ClimateChangeXplorers/xplorer-manual/build/stl/atmos/rs_screen_ring.stl

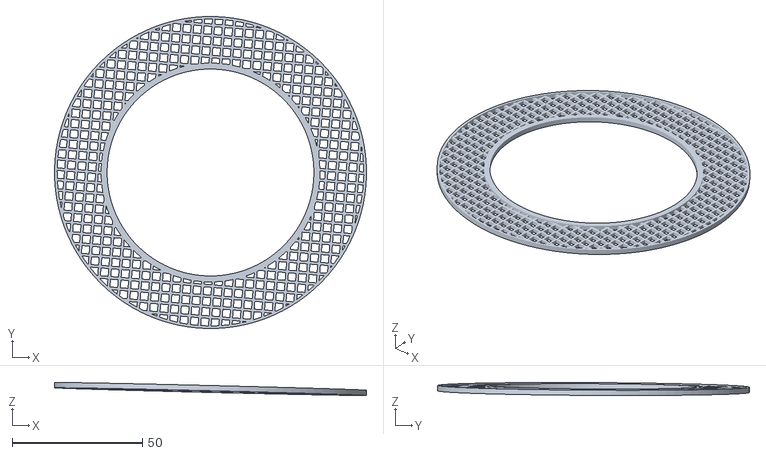
[picture p15: CAD file, 2020-08-12]
build/stl/atmos/rs_screen_ring.stl
120.0 x 120.0 x 5.02
