ClimateChangeXplorers/xplorer-manual/build/stl/hydro/hyd_rain_guage.stl

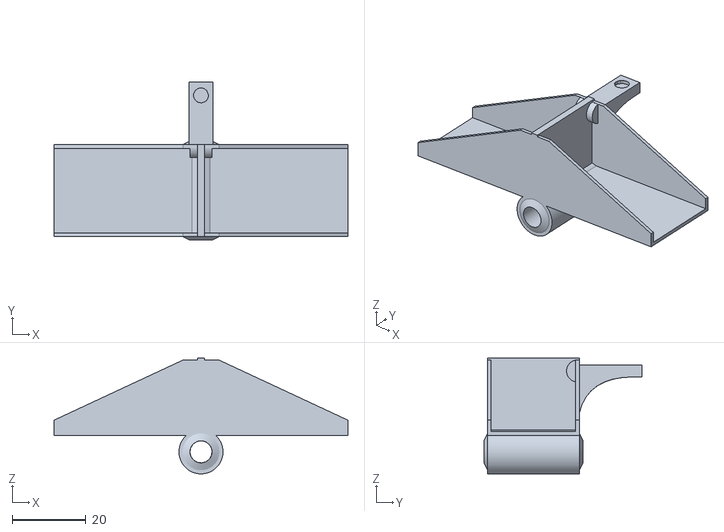
[picture p16: CAD file, 2020-07-23]
build/stl/hydro/hyd_rain_guage.stl
80.0 x 43.1 x 31.5
