ClimateChangeXplorers/xplorer-manual/build/stl/pvc/pvc_tripod_base_3.stl

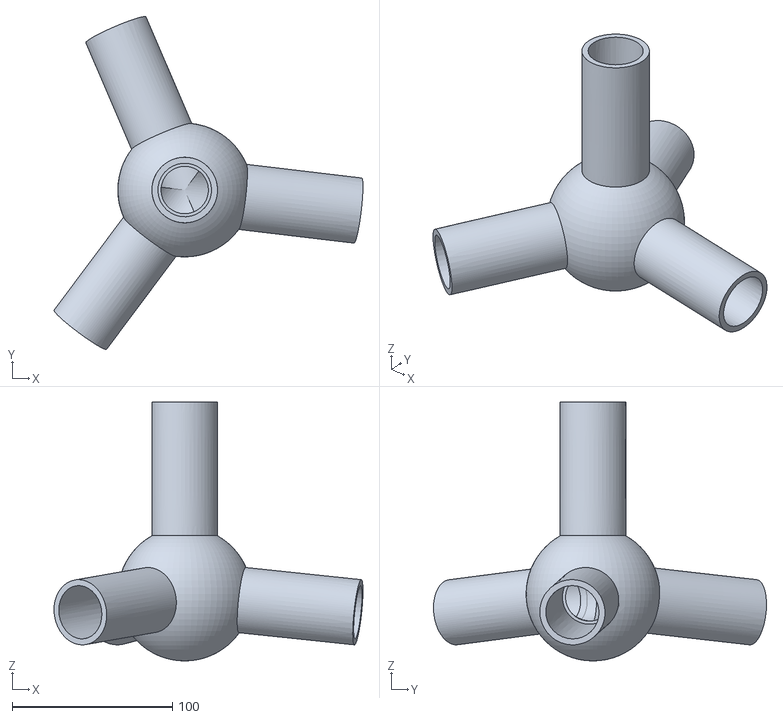
[picture p17: CAD file, 2021-01-25]
build/stl/pvc/pvc_tripod_base_3.stl
193.1 x 208.1 x 161.8
