ClimateChangeXplorers/xplorer-manual/build/stl/atmos/rs_base_plate.stl

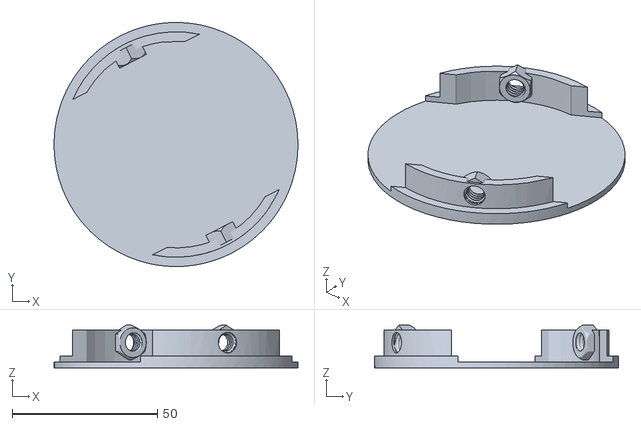
[picture p18: CAD file, 2020-08-12]
build/stl/atmos/rs_base_plate.stl
83.9 x 83.9 x 14.6
