ClimateChangeXplorers/xplorer-manual/build/stl/atmos/rs_top_leaf.stl

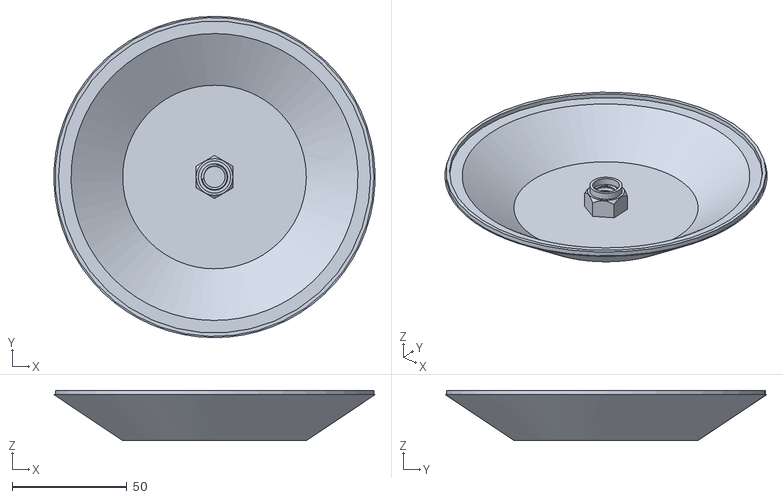
[picture p20: CAD file, 2020-07-23]
build/stl/atmos/rs_top_leaf.stl
139.8 x 139.9 x 21.9
