ClimateChangeXplorers/xplorer-manual/build/stl/pvc/pvc_stake.stl

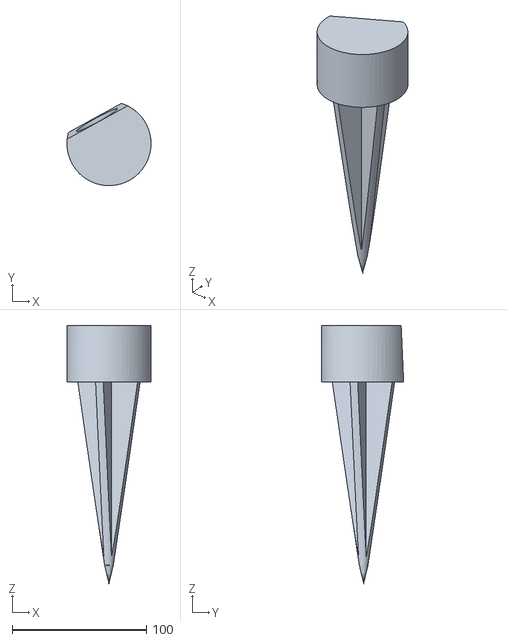
[picture p21: CAD file, 2020-11-06]
build/stl/pvc/pvc_stake.stl
62.7 x 61.4 x 192.5
