ClimateChangeXplorers/xplorer-manual/build/stl/atmos/rs_center_screen.stl

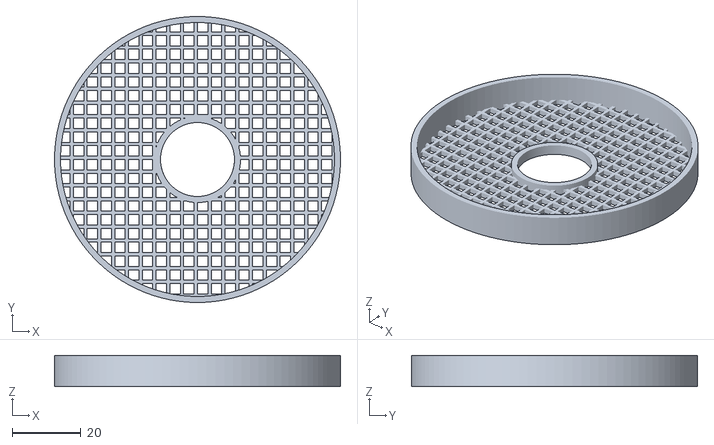
[picture p22: CAD file, 2020-07-23]
build/stl/atmos/rs_center_screen.stl
83.0 x 83.0 x 9.00
