ClimateChangeXplorers/xplorer-manual/build/stl/atmos/rs_single_leaf.stl

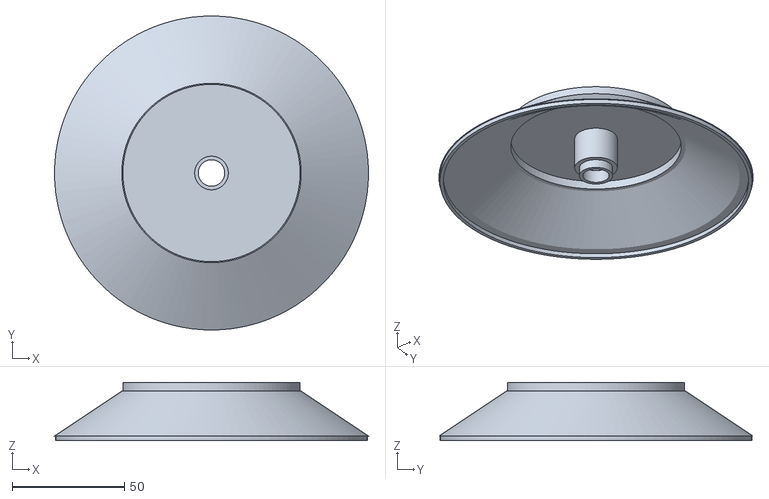
[picture p24: CAD file, 2020-07-23]
build/stl/atmos/rs_single_leaf.stl
140.0 x 140.0 x 25.9
