ClimateChangeXplorers/xplorer-manual/build/stl/pvc/pvc_en_tube.stl

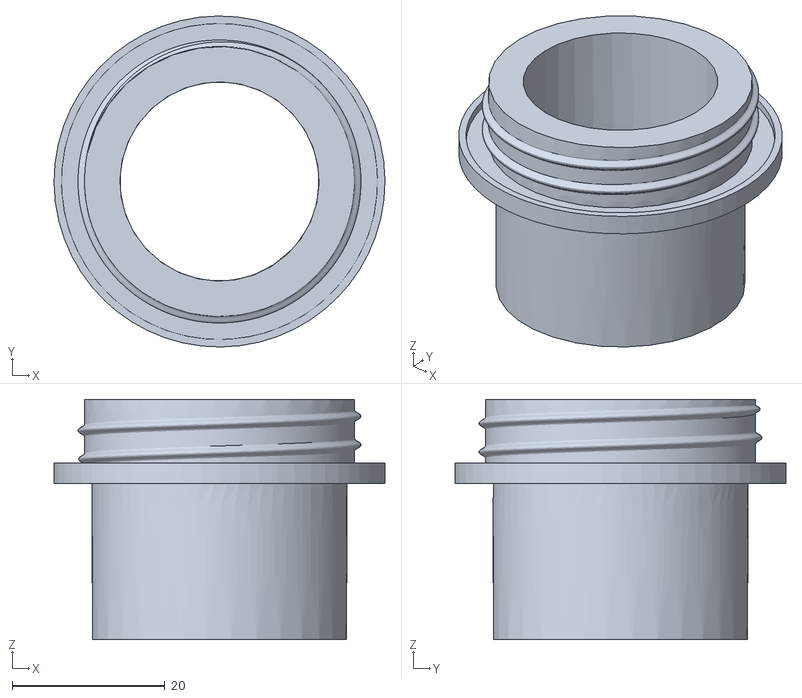
[picture p25: CAD file, 2020-11-06]
build/stl/pvc/pvc_en_tube.stl
43.4 x 43.4 x 31.4
