ClimateChangeXplorers/xplorer-manual/build/stl/atmos/rs_shaft.stl

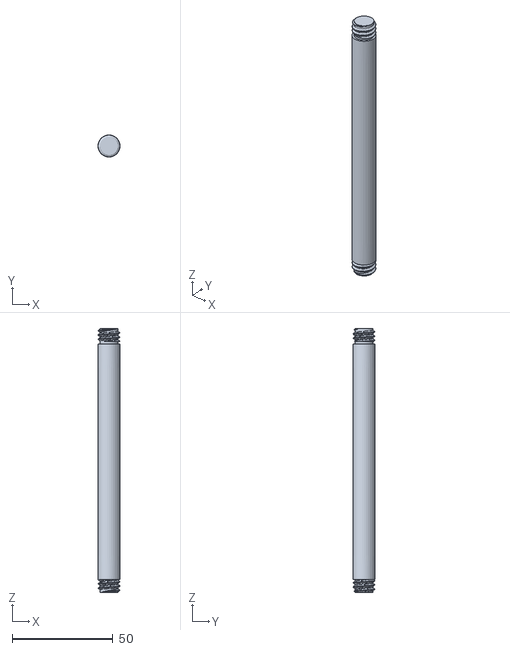
[picture p26: CAD file, 2020-07-23]
build/stl/atmos/rs_shaft.stl
11.0 x 11.0 x 131.2
