ClimateChangeXplorers/xplorer-manual/build/stl/pvc/pvc_en_cap.stl

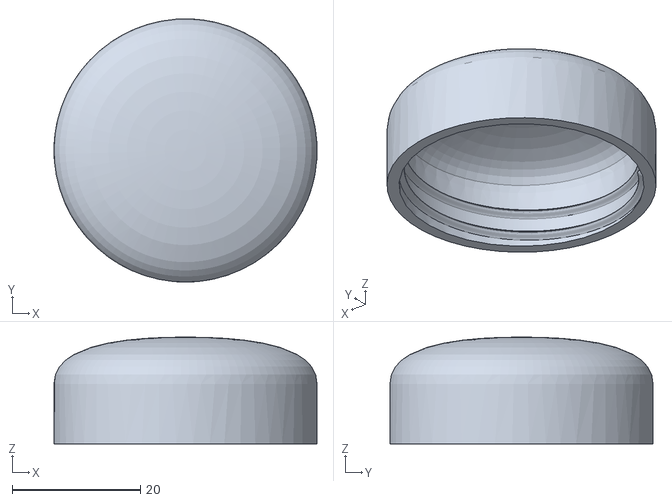
[picture p27: CAD file, 2020-11-06]
build/stl/pvc/pvc_en_cap.stl
41.0 x 41.0 x 16.6
