ClimateChangeXplorers/xplorer-manual/build/stl/atmos/rs_base.stl

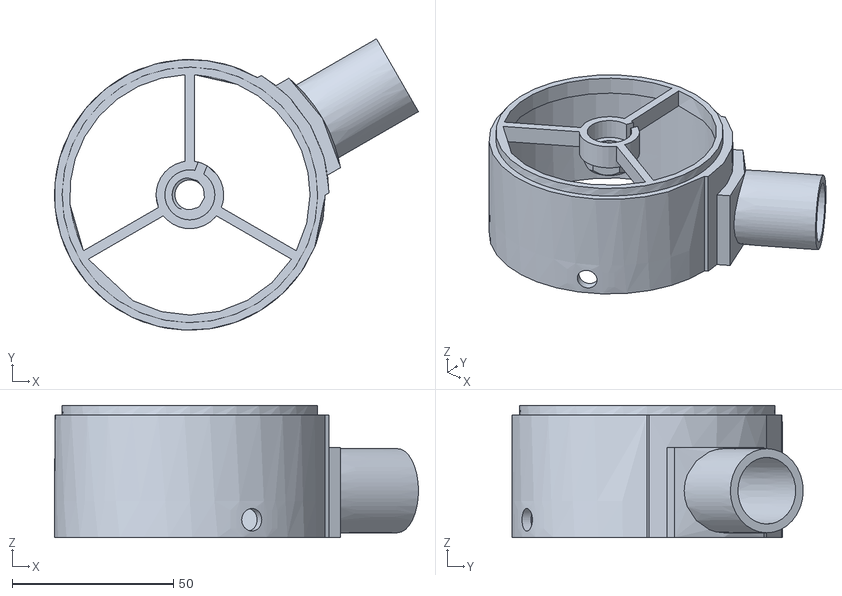
[picture p28: CAD file, 2020-07-23]
build/stl/atmos/rs_base.stl
112.8 x 90.3 x 41.0
