ClimateChangeXplorers/xplorer-manual/build/stl/pvc/pvc_tri_splitter.stl

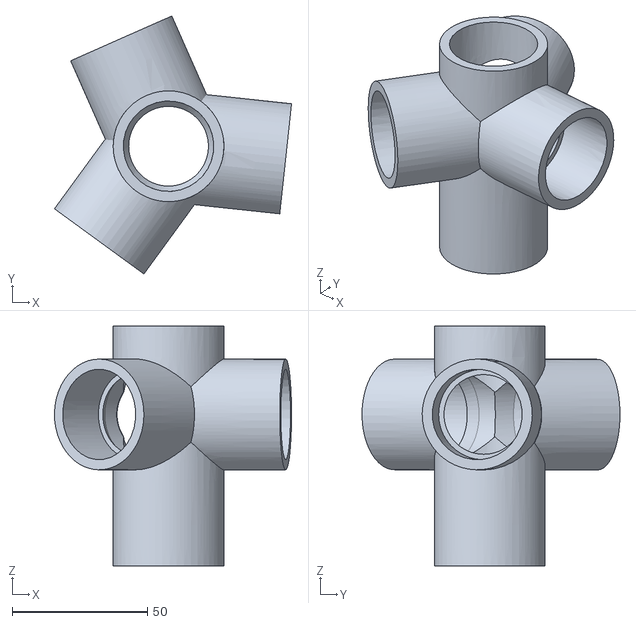
[picture p29: CAD file, 2020-11-06]
build/stl/pvc/pvc_tri_splitter.stl
87.8 x 95.5 x 88.8
