ClimateChangeXplorers/xplorer-manual/build/stl/atmos/rs_clip.stl

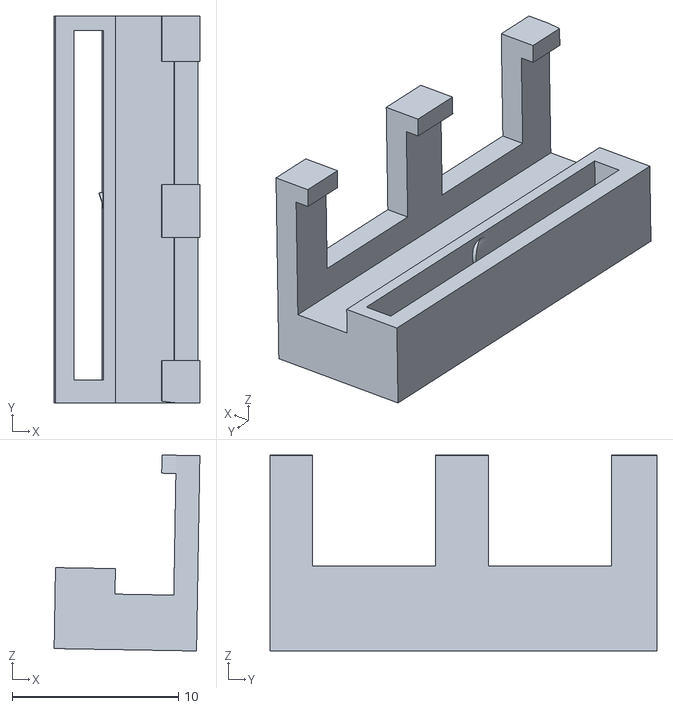
[picture p30: CAD file, 2020-07-23]
build/stl/atmos/rs_clip.stl
8.76 x 23.3 x 11.8
