ClimateChangeXplorers/xplorer-manual/build/stl/pvc/pvc_micro_holder.stl

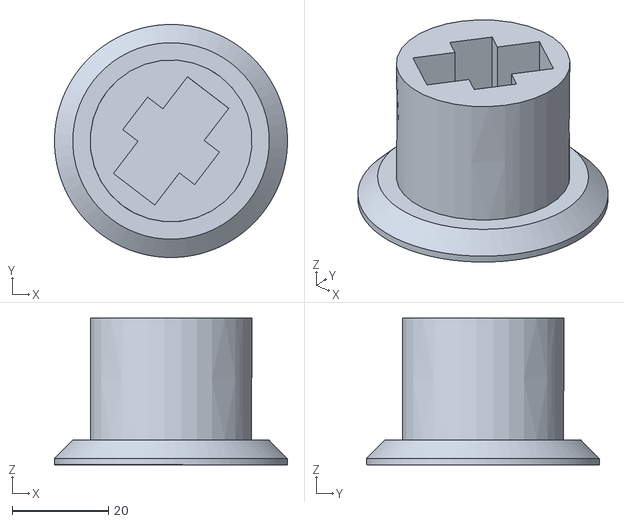
[picture p31: CAD file, 2020-08-13]
build/stl/pvc/pvc_micro_holder.stl
48.5 x 48.5 x 30.6
