ClimateChangeXplorers/xplorer-manual/build/stl/pvc/pvc_outerlock.stl

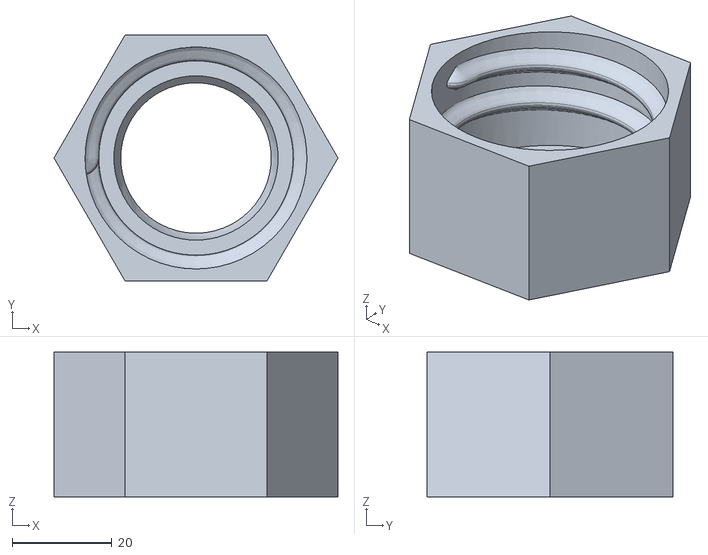
[picture p32: CAD file, 2020-08-13]
build/stl/pvc/pvc_outerlock.stl
56.9 x 49.3 x 29.0
