ClimateChangeXplorers/xplorer-manual/build/stl/pvc/pvc_innerlock.stl

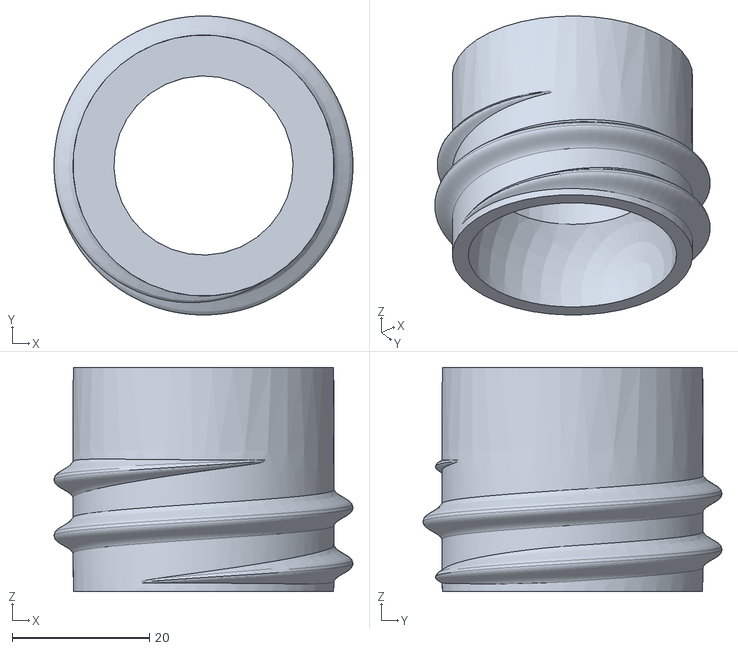
[picture p33: CAD file, 2020-08-13]
build/stl/pvc/pvc_innerlock.stl
43.5 x 43.5 x 32.6
