ClimateChangeXplorers/xplorer-manual/build/stl/pvc/pvc_balljoint_bar.stl

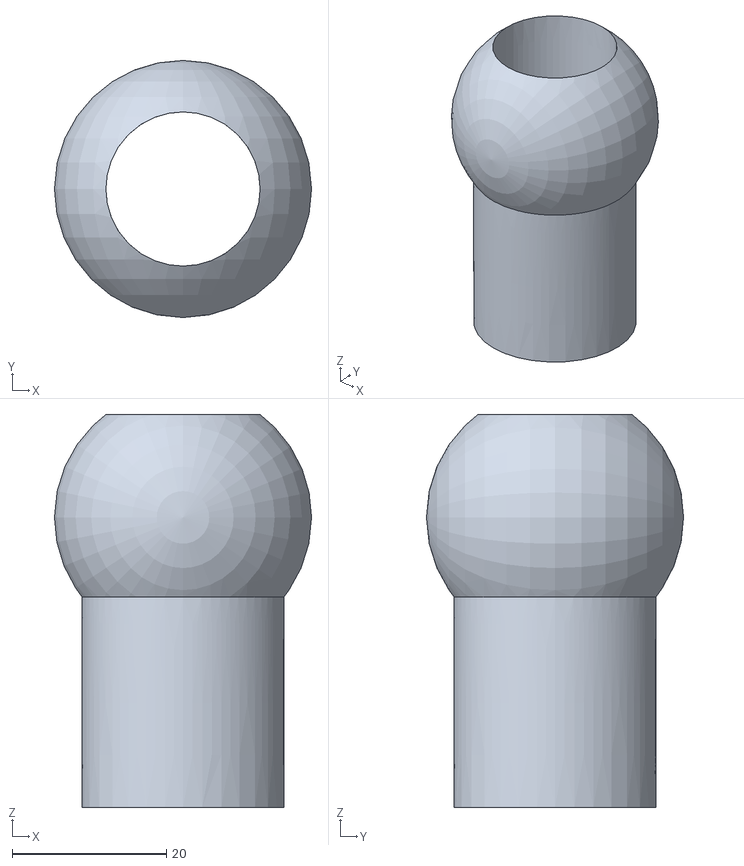
[picture p34: CAD file, 2020-08-13]
build/stl/pvc/pvc_balljoint_bar.stl
33.3 x 33.3 x 50.9
